InnoGreenTech/Home_controller/Board_VMC_home/Soft_VMC_home/Temp_Hum.ino

void get_sensors(){
  


  


  if (millis()-aquisition>4000) // si derniére aquisition date de deux secondes
  
  { 

    

    
     tIn= dht_in.readTemperature(); //lecture de la température en °
     hIn= dht_in.readHumidity(); // Lecture de l'humidité

     tOut=bme_out.readTempC();
     

     pOut=bme_out.readFloatPressure()/100;

     //Serial.println(pOut);
     //Serial.println(tOut);
     
     hOut=bme_out.readFloatHumidity();
     //Serial.println(hOut);

     qIn=read_co2();

        
     aquisition=millis();
  }
  
}
