InnoGreenTech/Home_controller/Soft_wifi_interface_home_controller/Recep_Infos.ino

void wamp_info(){
              if ( server.hasArg("temp_salon")) 
              {      
                String decodage=server.arg("PASSWORD");
                tsalon= decodage.toFloat();
                send_data();
              } 
                }
